jmding8/MercuryKeyboard/images/mercury.jpg

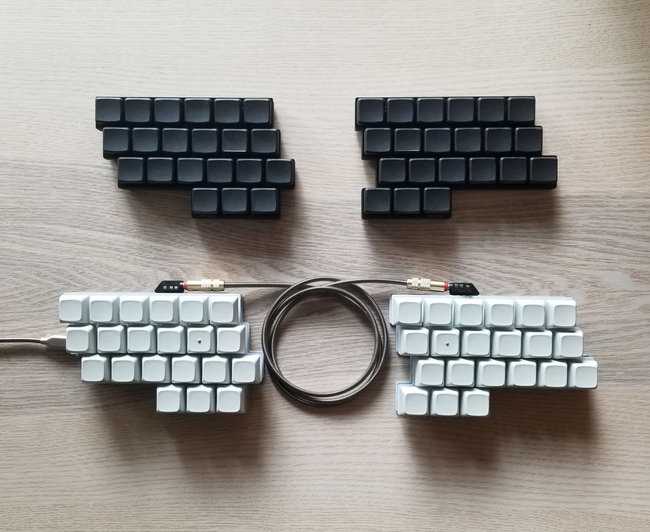
images/mercury.jpg
